baba2712/smart-helmet-with-anc/sim/results/spectra_compressor.png

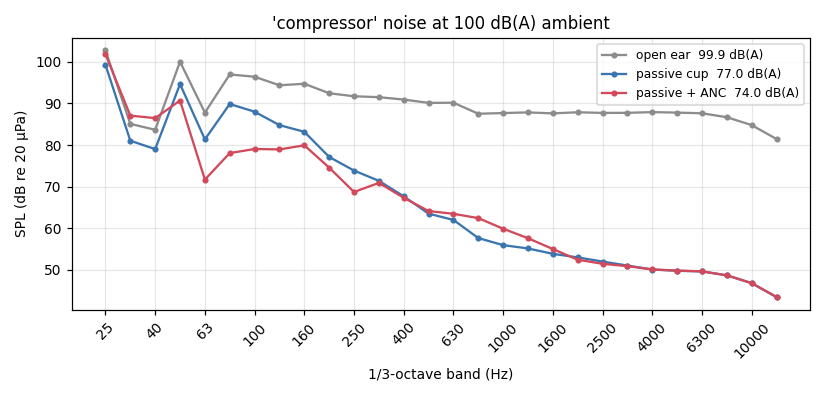
sim/results/spectra_compressor.png
