baba2712/smart-helmet-with-anc/sim/results/spectra_motor.png

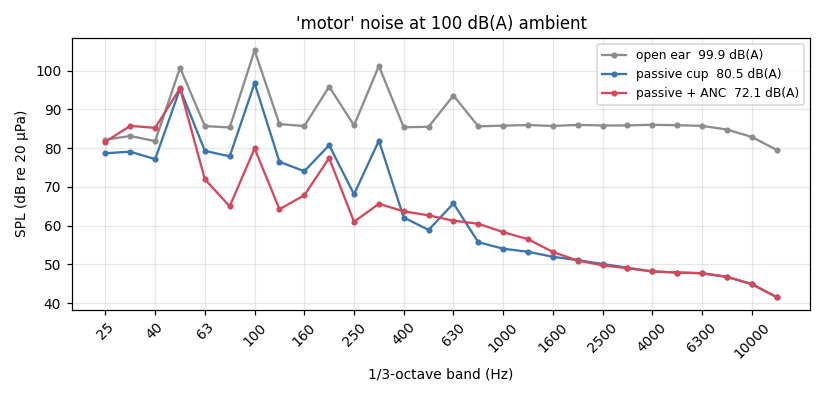
sim/results/spectra_motor.png
