baba2712/smart-helmet-with-anc/sim/results/spectra_pink.png

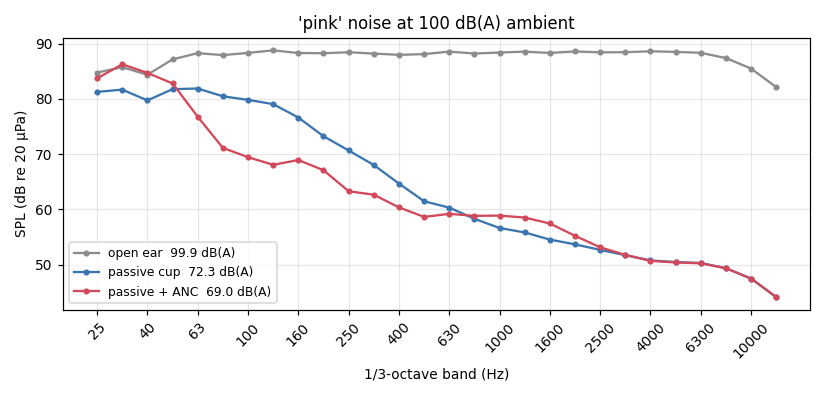
sim/results/spectra_pink.png
