baba2712/smart-helmet-with-anc/hardware/spice/results/driver.png

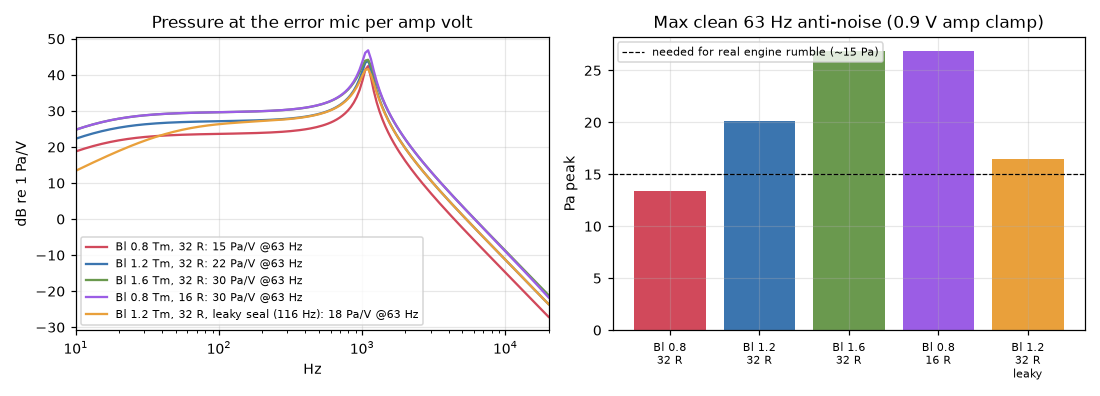
hardware/spice/results/driver.png
