baba2712/smart-helmet-with-anc/hardware/spice/results/frontend.png

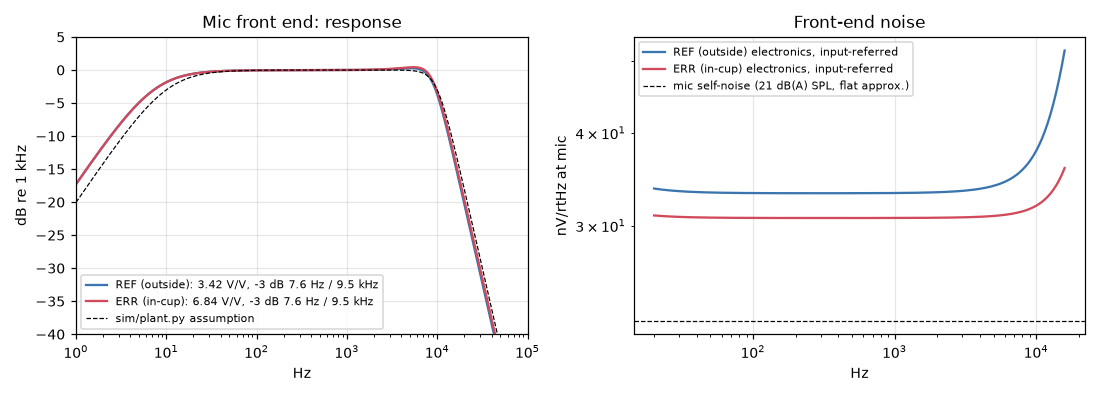
hardware/spice/results/frontend.png
