baba2712/smart-helmet-with-anc/hardware/spice/results/recon.png

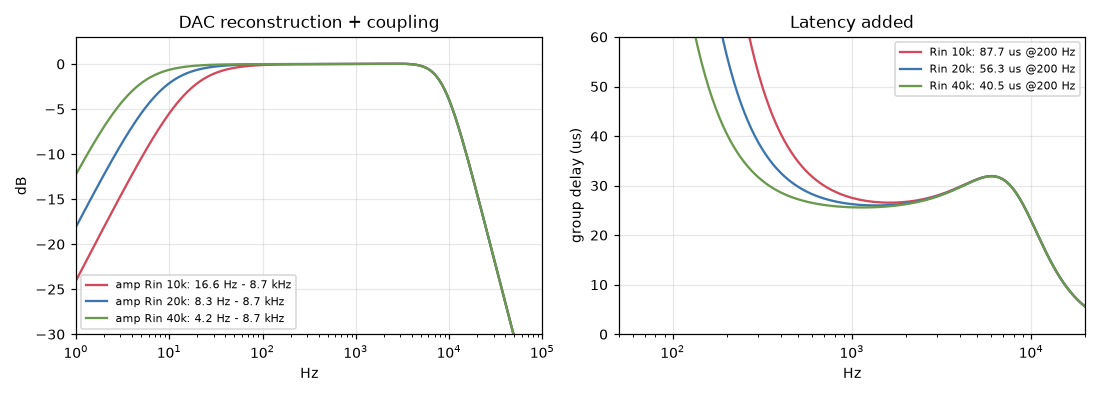
hardware/spice/results/recon.png
