baba2712/smart-helmet-with-anc/hardware/spice/results/vmid.png

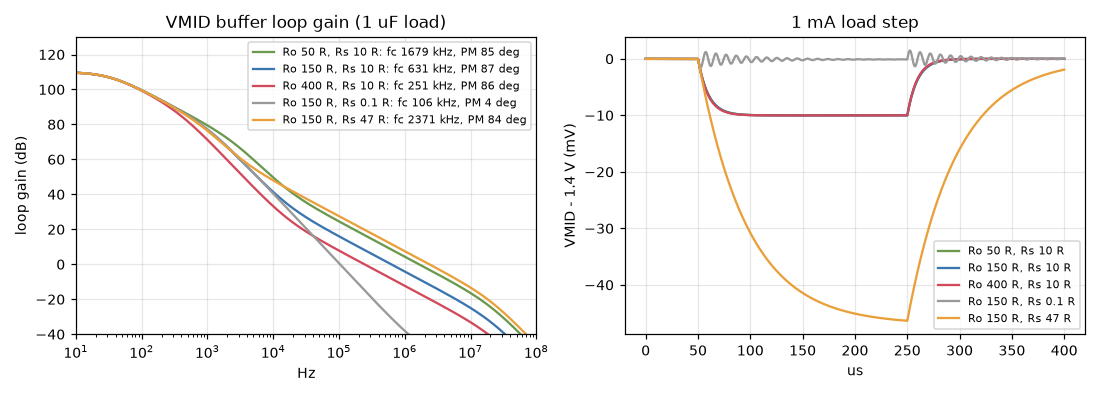
hardware/spice/results/vmid.png
