baba2712/smart-helmet-with-anc/sim/results/convergence.png

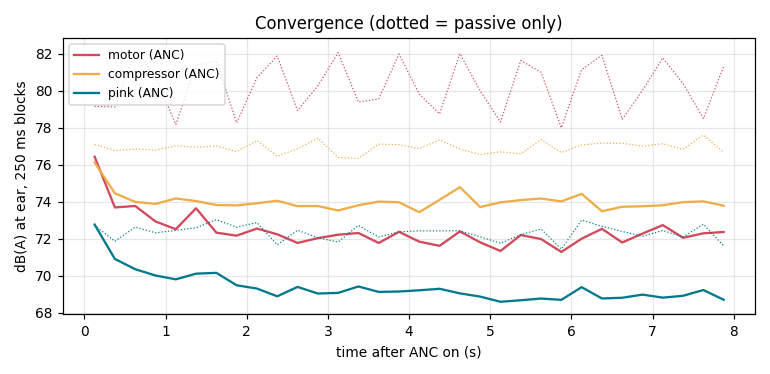
sim/results/convergence.png
