baba2712/smart-helmet-with-anc/sim/results/latency_sweep.png

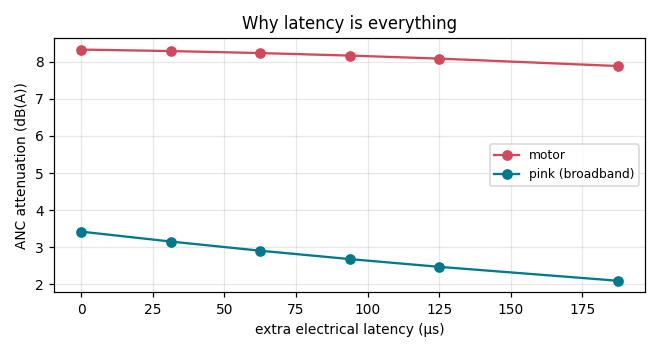
sim/results/latency_sweep.png
