baba2712/smart-helmet-with-anc/sim/results/paths.png

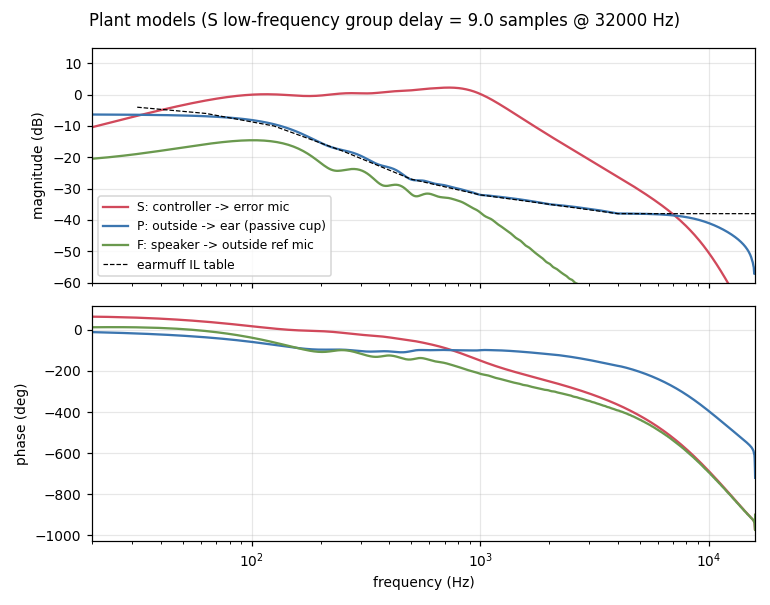
sim/results/paths.png
