baba2712/smart-helmet-with-anc/sim/results/robustness.png

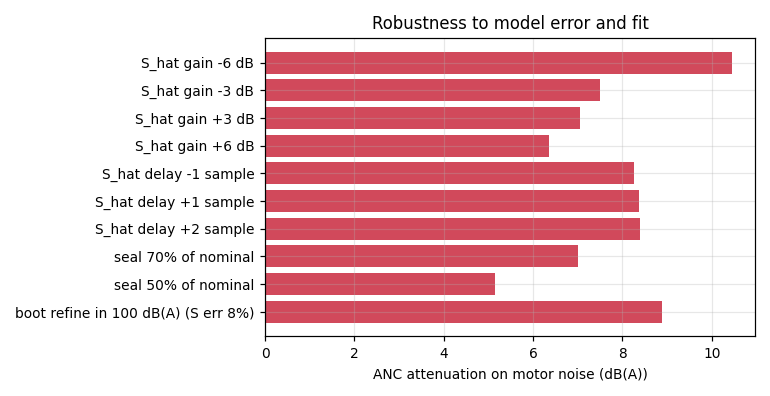
sim/results/robustness.png
