baba2712/smart-helmet-with-anc/sim/results/seal_monitor.png

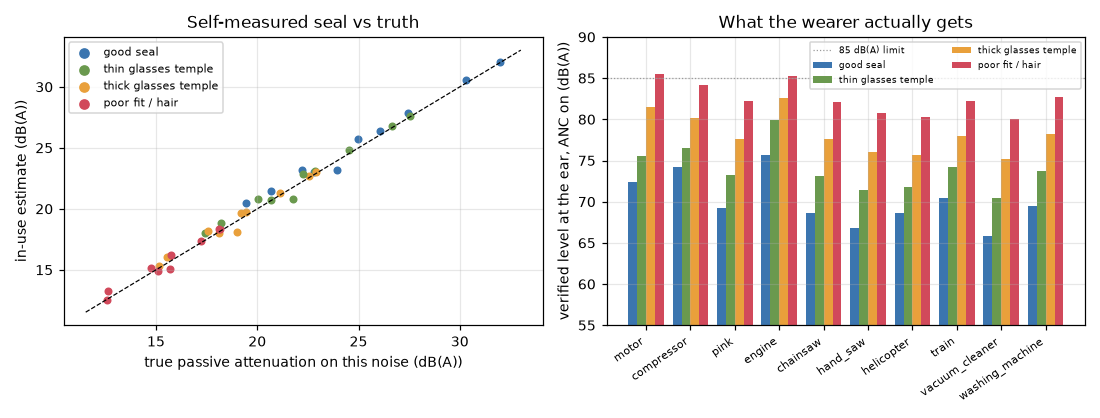
sim/results/seal_monitor.png
