baba2712/smart-helmet-with-anc/hardware/gen/pinmap.py

"""STM32H743VIT6 (LQFP-100) pin assignment - single source of truth.

Used by the schematic generator (main board nets) and emitted as
firmware/inc/board_pins.h so hardware and firmware can never disagree.
Run:  python3 pinmap.py   (rewrites the header)
"""
import os

# net name -> (port pin, LQFP100 pin number, function / alternate, note)
PINS = {
    # ---- audio: ADC1/ADC2 dual simultaneous, DAC1 ----
    "REF_L":      ("PA6",  30, "ADC12_INP3",  "left outside (reference) mic"),
    "ERR_L":      ("PC4",  32, "ADC12_INP4",  "left inside (error) mic"),
    "REF_R":      ("PB0",  34, "ADC12_INP9",  "right reference mic (via satellite board)"),
    "ERR_R":      ("PC5",  33, "ADC12_INP8",  "right error mic (via satellite board)"),
    "DAC_L":      ("PA4",  28, "DAC1_OUT1",   "left anti-noise out -> recon filter -> amp"),
    "DAC_R":      ("PA5",  29, "DAC1_OUT2",   "right anti-noise out"),
    "VBAT_SNS":   ("PC0",  15, "ADC3_INP10",  "battery / 2"),
    # ---- USB-C (OTG FS) ----
    "USB_DM":     ("PA11", 70, "AF10",        "USB2_OTG_FS DM"),
    "USB_DP":     ("PA12", 71, "AF10",        "USB2_OTG_FS DP"),
    "VBUS_SNS":   ("PA9",  68, "GPIO_IN",     "VBUS * 0.5 (USB present)"),
    # ---- debug ----
    "SWDIO":      ("PA13", 72, "SWD",         ""),
    "SWCLK":      ("PA14", 76, "SWD",         ""),
    "SWO":        ("PB3",  89, "SWO",         ""),
    "DBG_TP":     ("PC8",  65, "GPIO_OUT",    "ISR timing test point"),
    # ---- clocks ----
    "HSE_IN":     ("PH0",  12, "OSC_IN",      "25 MHz crystal"),
    "HSE_OUT":    ("PH1",  13, "OSC_OUT",     ""),
    # ---- UI ----
    "BTN":        ("PC13",  7, "GPIO_IN_PU",  "power/mode button sense via NPN inverter, active low"),
    "LED_R":      ("PE9",  39, "TIM1_CH1",    "RGB LED, common anode, active low"),
    "LED_G":      ("PE11", 41, "TIM1_CH2",    ""),
    "LED_B":      ("PE13", 43, "TIM1_CH3",    ""),
    # ---- power management ----
    "PWR_HOLD":   ("PD4",  85, "GPIO_OUT",    "keeps the buck-boost enabled after the button is released"),
    "CHG_STAT":   ("PD2",  83, "GPIO_IN_PU",  "MCP73831 STAT: low = charging"),
    # ---- headphone amp TPA6132A2 ----
    "AMP_EN":     ("PD0",  81, "GPIO_OUT",    "amp enable (mute when low)"),
    "AMP_G0":     ("PD1",  82, "GPIO_OUT",    "amp gain select bit 0"),
    "AMP_G1":     ("PD3",  84, "GPIO_OUT",    "amp gain select bit 1"),
    # ---- BLE module (optional, UART) ----
    "BLE_TX":     ("PD8",  55, "USART3_TX AF7", "MCU TX -> module RX"),
    "BLE_RX":     ("PD9",  56, "USART3_RX AF7", "module TX -> MCU RX"),
    "BLE_EN":     ("PD10", 57, "GPIO_OUT",    "module enable / reset (high = run)"),
    "BLE_STATE":  ("PD11", 58, "GPIO_IN",     "module 'connected' status"),
    # ---- spare / expansion (test pads) ----
    "I2C1_SCL":   ("PB6",  92, "AF4",         "spare, test pad (fuel gauge option)"),
    "I2C1_SDA":   ("PB7",  93, "AF4",         "spare, test pad"),
}


def header():
    L = ["/* AUTO-GENERATED by hardware/gen/pinmap.py - the schematic uses the same table. */",
         "#ifndef BOARD_PINS_H", "#define BOARD_PINS_H", ""]
    for net, (pin, num, fn, note) in PINS.items():
        port, idx = pin[1], int(pin[2:])
        L.append(f"#define PIN_{net}_PORT  GPIO{port}   /* {pin} (LQFP100 #{num}) {fn}{' - ' + note if note else ''} */")
        L.append(f"#define PIN_{net}_PIN   {idx}u")
    L += ["", "#endif", ""]
    return "\n".join(L)


if __name__ == "__main__":
    out = os.path.join(os.path.dirname(__file__), "..", "..", "firmware", "inc", "board_pins.h")
    with open(out, "w") as fh:
        fh.write(header())
    print("wrote", os.path.normpath(out))
